bazsimarkus/avr-basic-sbc/pc-tools/sbc-studio/sbc-studio-output/bitmap-editor/dog.jpg

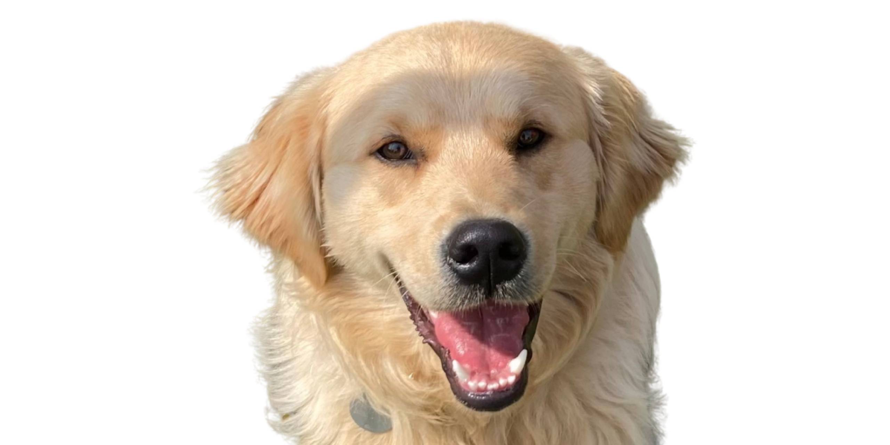
pc-tools/sbc-studio/sbc-studio-output/bitmap-editor/dog.jpg
